nightgryphon/LInTech-network/Server-IBM-PC/Reference_Photo/MCU_Night_Gryphon.jpeg

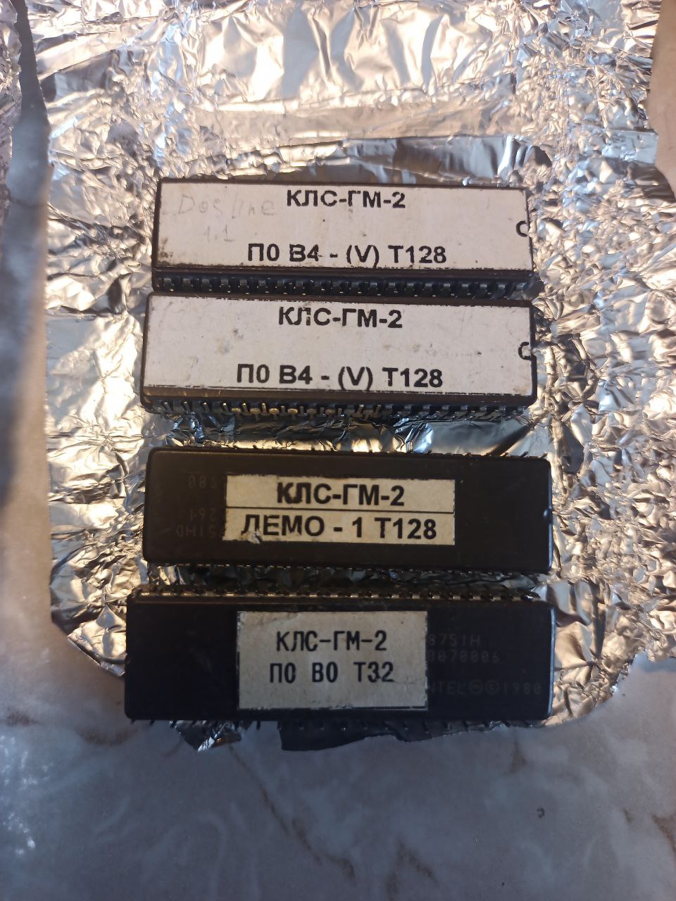
Server-IBM-PC/Reference_Photo/MCU_Night_Gryphon.jpeg
