nightgryphon/LInTech-network/Server-IBM-PC/Reference_Photo/NC-ACM-2.2-1994_Arseny-UKNC.narod.ru/01_NC-ACM-2.2-1994_Front_Photo.jpg

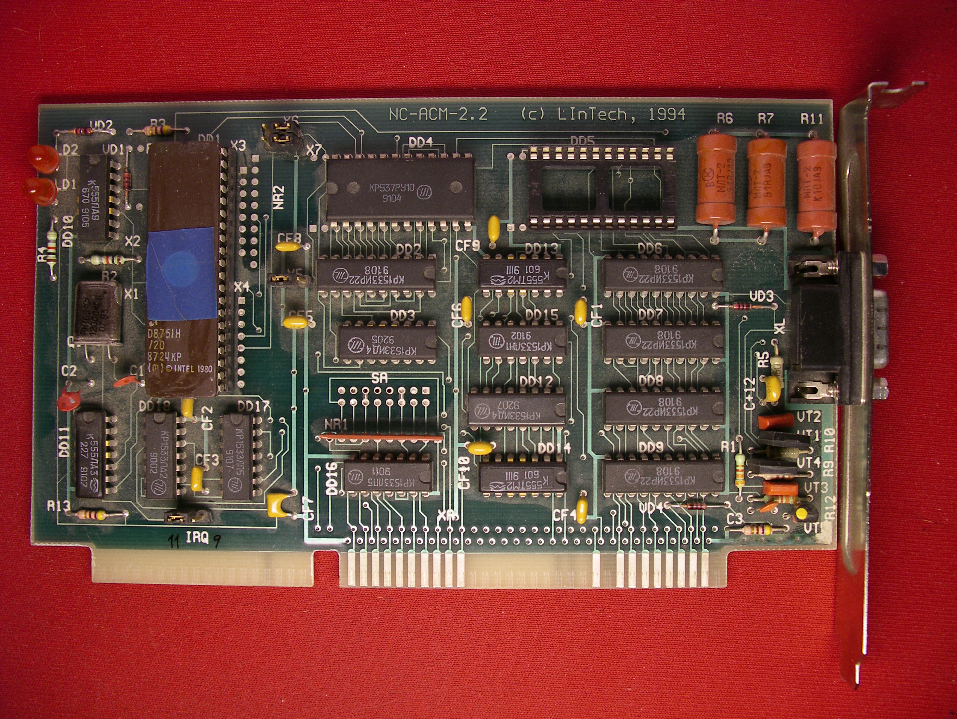
Server-IBM-PC/Reference_Photo/NC-ACM-2.2-1994_Arseny-UKNC.narod.ru/01_NC-ACM-2.2-1994_Front_Photo.jpg
