nightgryphon/LInTech-network/Server-IBM-PC/Reference_Photo/NC-ACM-2.2-1994_Arseny-UKNC.narod.ru/02_NC-ACM-2.2-1994_Back_Photo.jpg

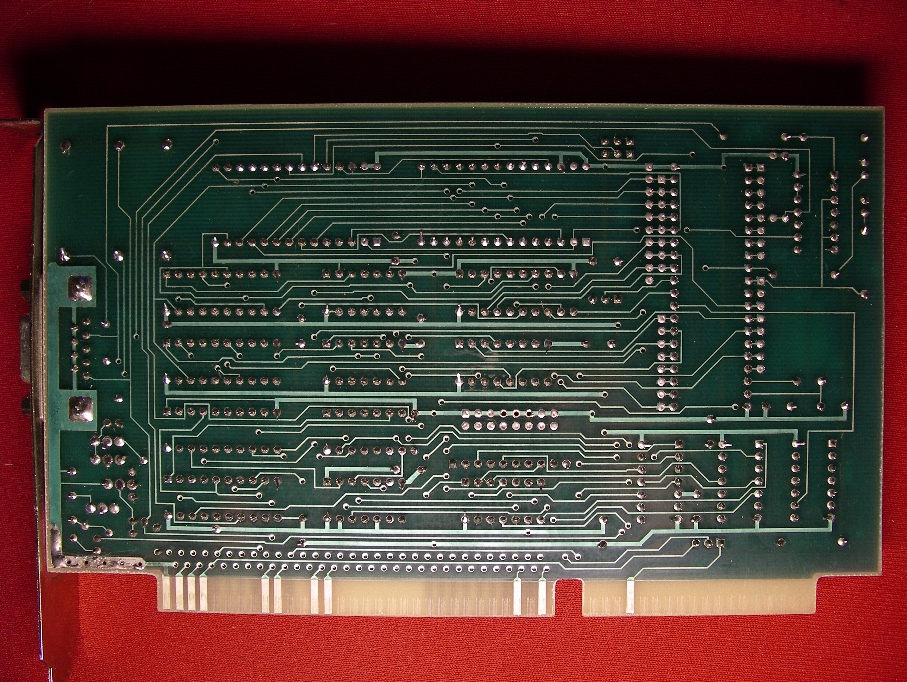
Server-IBM-PC/Reference_Photo/NC-ACM-2.2-1994_Arseny-UKNC.narod.ru/02_NC-ACM-2.2-1994_Back_Photo.jpg
