nightgryphon/LInTech-network/Server-IBM-PC/Reference_Photo/NC-ACM-2.2-1994_Arseny-UKNC.narod.ru/03_NC-ACM-2.2-1994_Front_Photo_Tracks.jpg

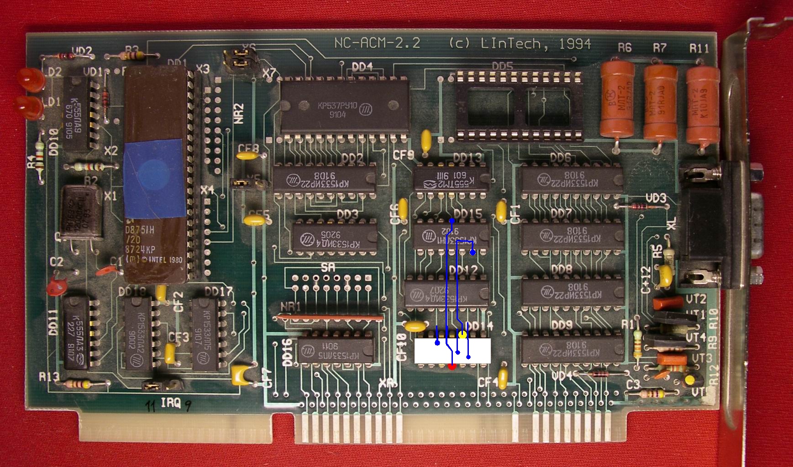
Server-IBM-PC/Reference_Photo/NC-ACM-2.2-1994_Arseny-UKNC.narod.ru/03_NC-ACM-2.2-1994_Front_Photo_Tracks.jpg
