nightgryphon/LInTech-network/Server-IBM-PC/Reference_Photo/NC-ACM-2.3E-1996_Serebriakov_aka_PaulArgent/05_NC-ACM-2.3E-1996_Front_Photo_MCU.jpg

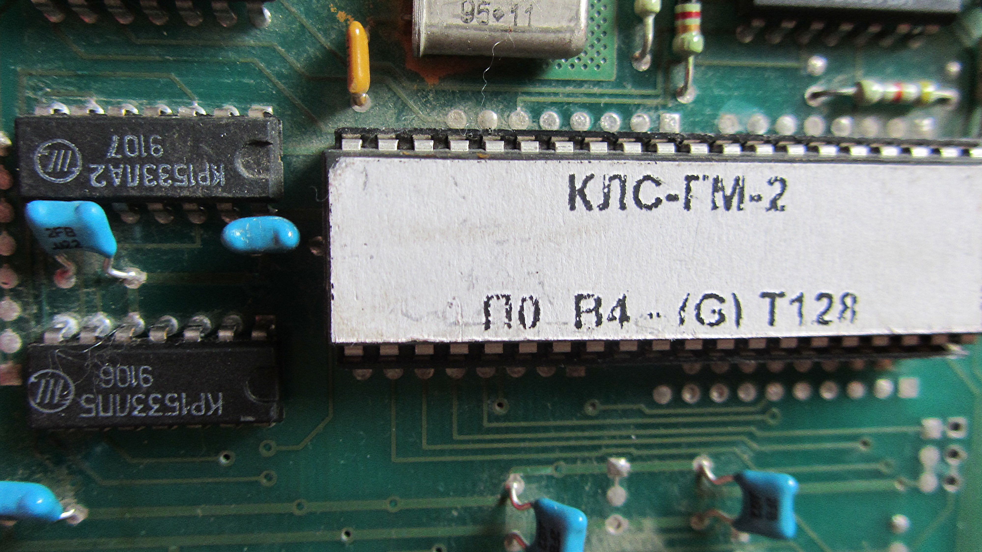
Server-IBM-PC/Reference_Photo/NC-ACM-2.3E-1996_Serebriakov_aka_PaulArgent/05_NC-ACM-2.3E-1996_Front_Photo_MCU.jpg
