nightgryphon/LInTech-network/Server-IBM-PC/Reference_Photo/NC-ACM-2.3E-1996_Serebriakov_aka_PaulArgent/07_NC-ACM-2.3E-1996_Back_Photo.jpg

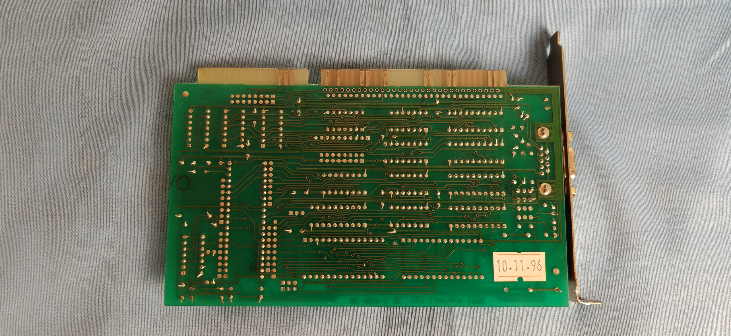
Server-IBM-PC/Reference_Photo/NC-ACM-2.3E-1996_Serebriakov_aka_PaulArgent/07_NC-ACM-2.3E-1996_Back_Photo.jpg
