nightgryphon/LInTech-network/Terminal-BK0010/Reference_Photo/NC-IFM-H1.0-1995_Night_Gryphon/02_NC-IFM-H1.0-1995-Back-Scan.jpg

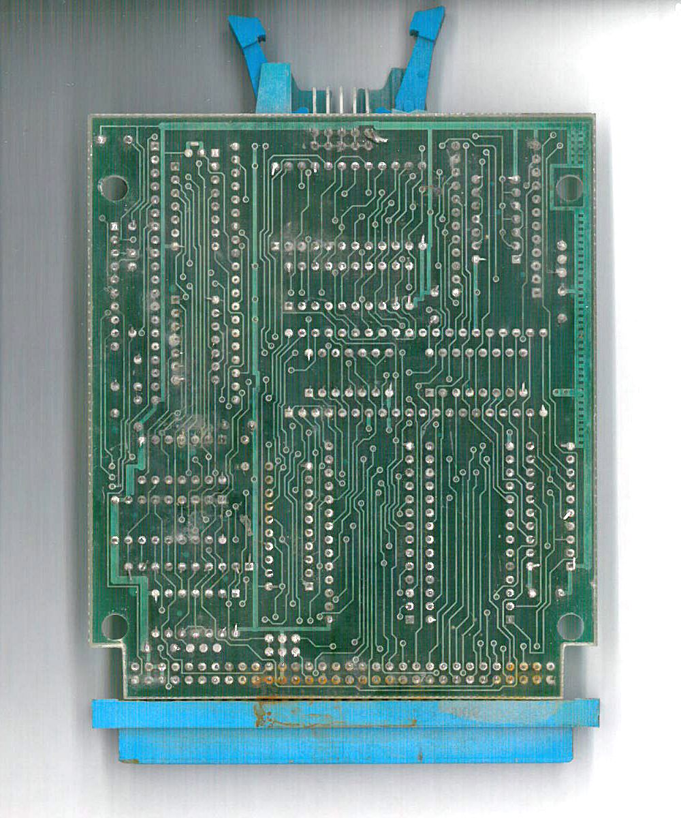
Terminal-BK0010/Reference_Photo/NC-IFM-H1.0-1995_Night_Gryphon/02_NC-IFM-H1.0-1995-Back-Scan.jpg
