nightgryphon/LInTech-network/Terminal-Corvette/Reference_Photo/NC-IFM-2.1-1993_Anton_Mironov_Front_MCU.jpg

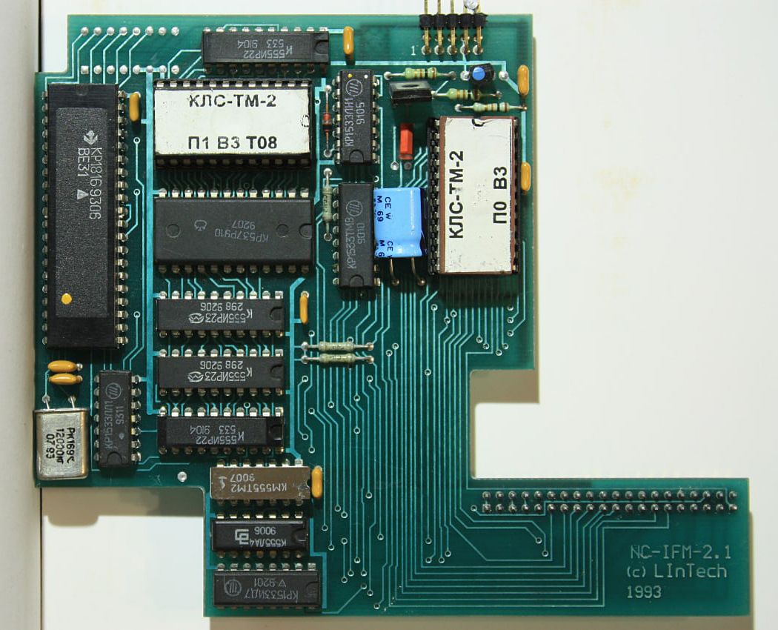
Terminal-Corvette/Reference_Photo/NC-IFM-2.1-1993_Anton_Mironov_Front_MCU.jpg
