nightgryphon/LInTech-network/Terminal-Corvette/Reference_Photo/NC-IFM-2.1-1993_lordamot_aka_Sergey_Lemeshev/01_NC-IFM-2.1-1993_Front_Scan.png

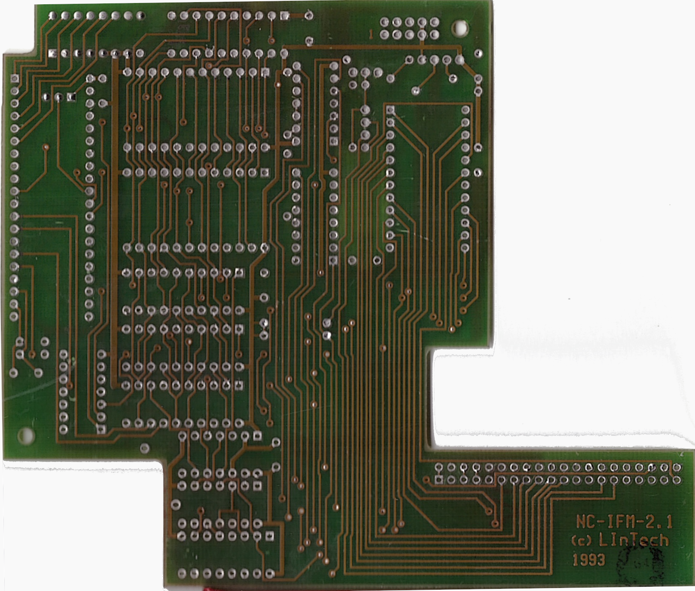
Terminal-Corvette/Reference_Photo/NC-IFM-2.1-1993_lordamot_aka_Sergey_Lemeshev/01_NC-IFM-2.1-1993_Front_Scan.png
