nightgryphon/LInTech-network/Terminal-Corvette/Reference_Photo/NC-IFM-2.1-1993_lordamot_aka_Sergey_Lemeshev/05_NC-IFM-2.1-1993_Photo_Connection.jpg

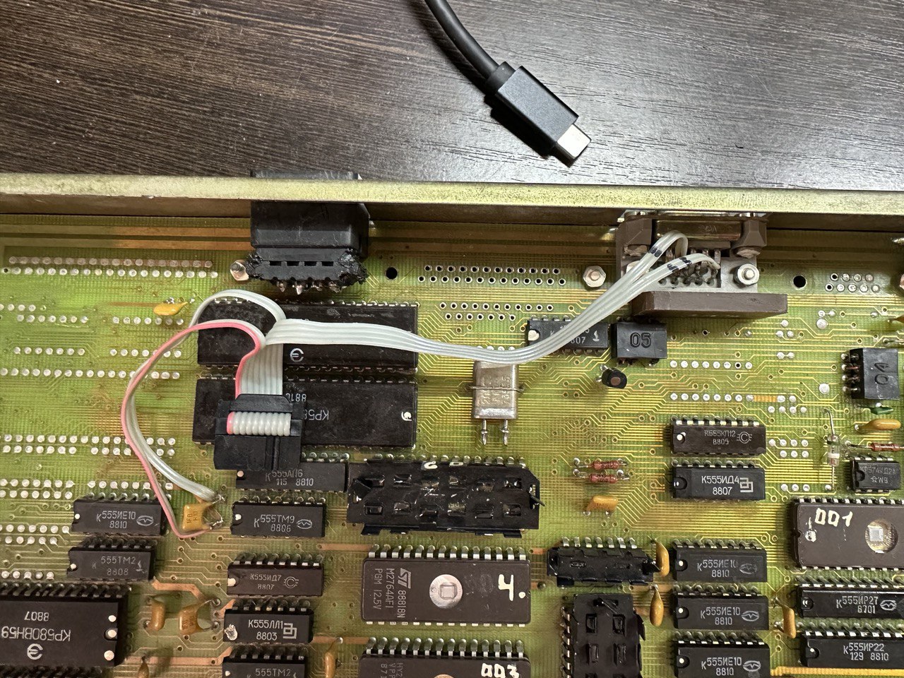
Terminal-Corvette/Reference_Photo/NC-IFM-2.1-1993_lordamot_aka_Sergey_Lemeshev/05_NC-IFM-2.1-1993_Photo_Connection.jpg
