nightgryphon/LInTech-network/Terminal-Corvette/Reference_Photo/NC-IFM-2.1-1993_lordamot_aka_Sergey_Lemeshev/07_NC-IFM-2.1-1993_Photo_EPROM-P1-Left.jpg

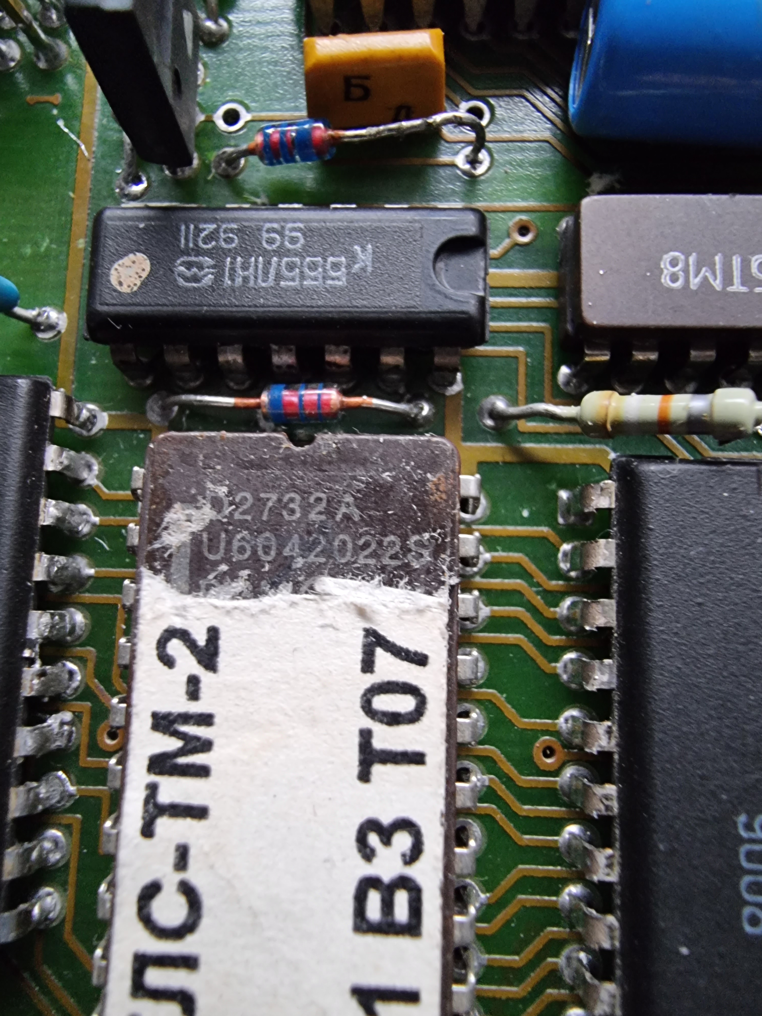
Terminal-Corvette/Reference_Photo/NC-IFM-2.1-1993_lordamot_aka_Sergey_Lemeshev/07_NC-IFM-2.1-1993_Photo_EPROM-P1-Left.jpg
