nightgryphon/LInTech-network/Terminal-UKNC/Reference_Photo/NC-IFM-B1.0-1994_Arseny-UKNC.narod.ru/NC-IFM-B1.0-1994_Front_Photo.jpg

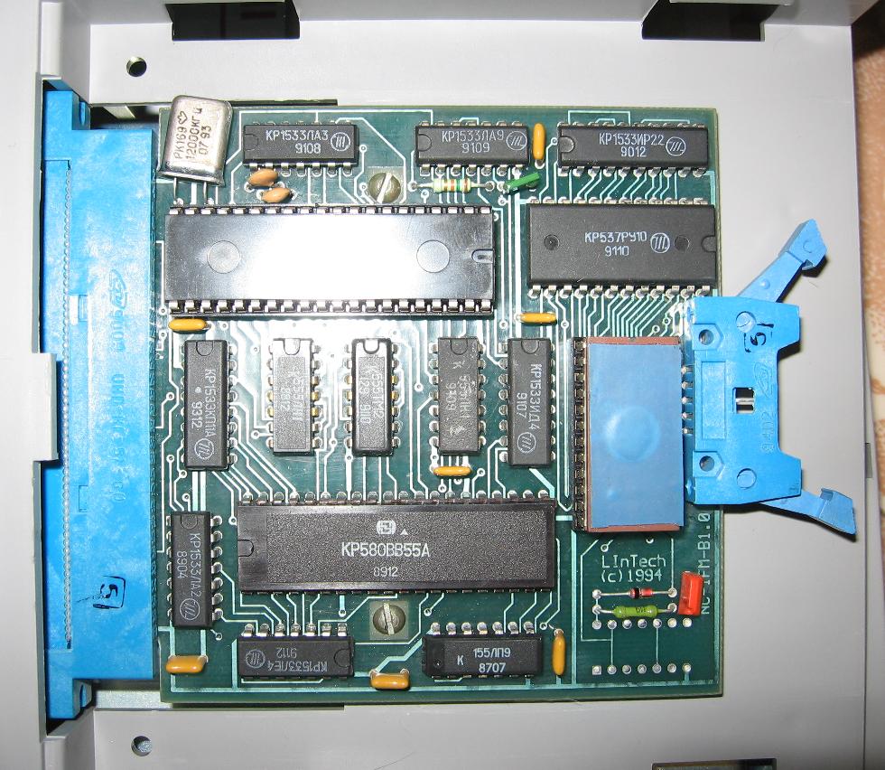
Terminal-UKNC/Reference_Photo/NC-IFM-B1.0-1994_Arseny-UKNC.narod.ru/NC-IFM-B1.0-1994_Front_Photo.jpg
