nightgryphon/LInTech-network/Terminal-UKNC/Reference_Photo/NC-IFM-B1.0-1994_Night_Gryphon/02_NC-IFM-B1.0-1994_Back_Scan.jpg

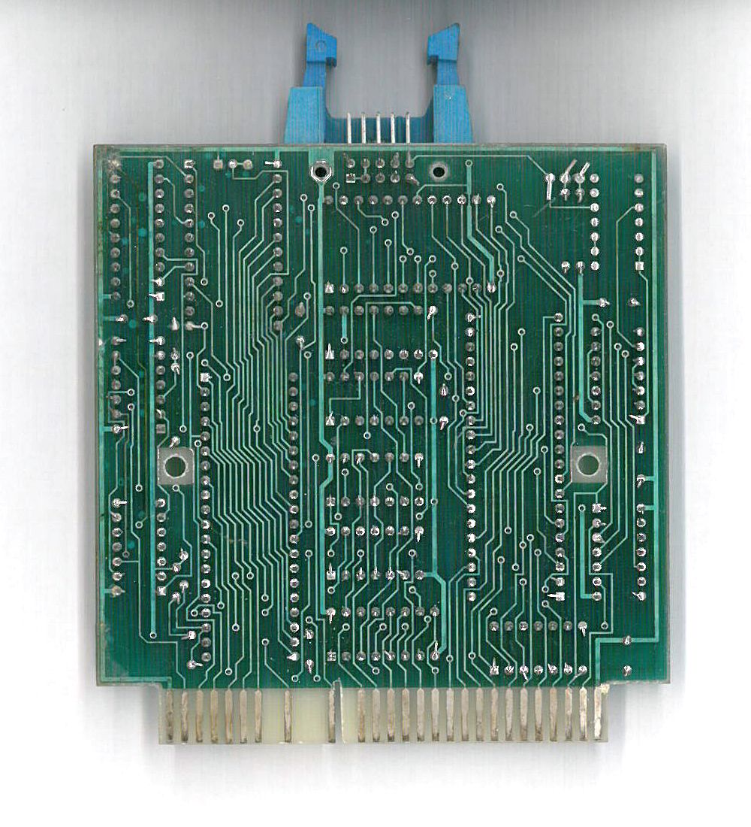
Terminal-UKNC/Reference_Photo/NC-IFM-B1.0-1994_Night_Gryphon/02_NC-IFM-B1.0-1994_Back_Scan.jpg
