nightgryphon/LInTech-network/Terminal-Corvette/Reference_Photo/NC-IFM-2.1-1993_Serebriakov_aka_PaulArgent/01_PCB_07.12.97-ONE_EPROM/07_NC-IFM-2.1-1993_Photo_Installed_new_label.jpg

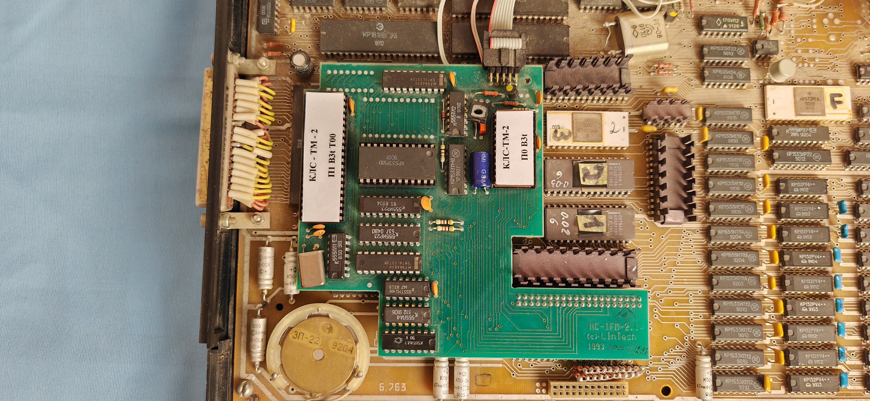
Terminal-Corvette/Reference_Photo/NC-IFM-2.1-1993_Serebriakov_aka_PaulArgent/01_PCB_07.12.97-ONE_EPROM/07_NC-IFM-2.1-1993_Photo_Installed_new_label.jpg
