nightgryphon/LInTech-network/Terminal-Corvette/Reference_Photo/NC-IFM-2.1-1993_Serebriakov_aka_PaulArgent/02_PCB_18.11.97/04_NC-IFM-2.1-1993_Photo_Installed.jpg

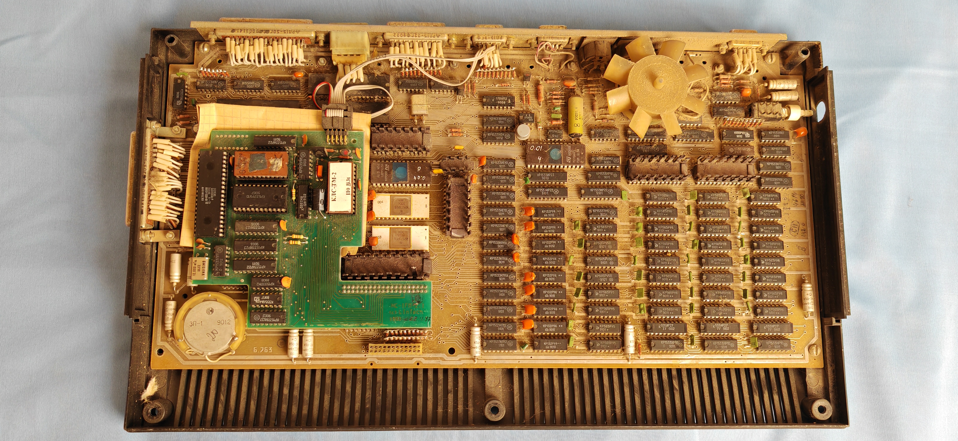
Terminal-Corvette/Reference_Photo/NC-IFM-2.1-1993_Serebriakov_aka_PaulArgent/02_PCB_18.11.97/04_NC-IFM-2.1-1993_Photo_Installed.jpg
