nightgryphon/LInTech-network/Terminal-Corvette/Reference_Photo/NC-IFM-2.1-1993_Serebriakov_aka_PaulArgent/03_PCB_13.11.97/03_NC-IFM-2.1-1993_Back_Scan.jpg

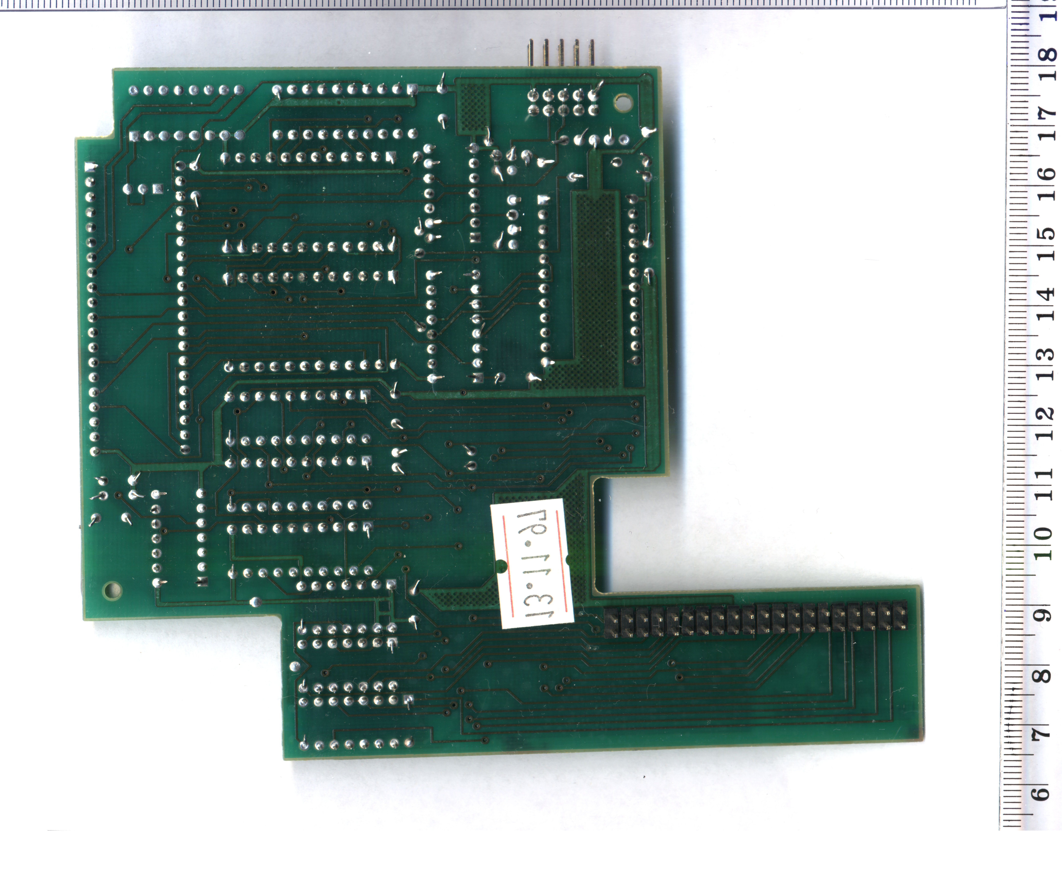
Terminal-Corvette/Reference_Photo/NC-IFM-2.1-1993_Serebriakov_aka_PaulArgent/03_PCB_13.11.97/03_NC-IFM-2.1-1993_Back_Scan.jpg
