nightgryphon/LInTech-network/Terminal-Corvette/Reference_Photo/NC-IFM-2.1-1993_Serebriakov_aka_PaulArgent/04_PCB_01.05.97/02_NC-IFM-2.1-1993_Front_Scan.jpg

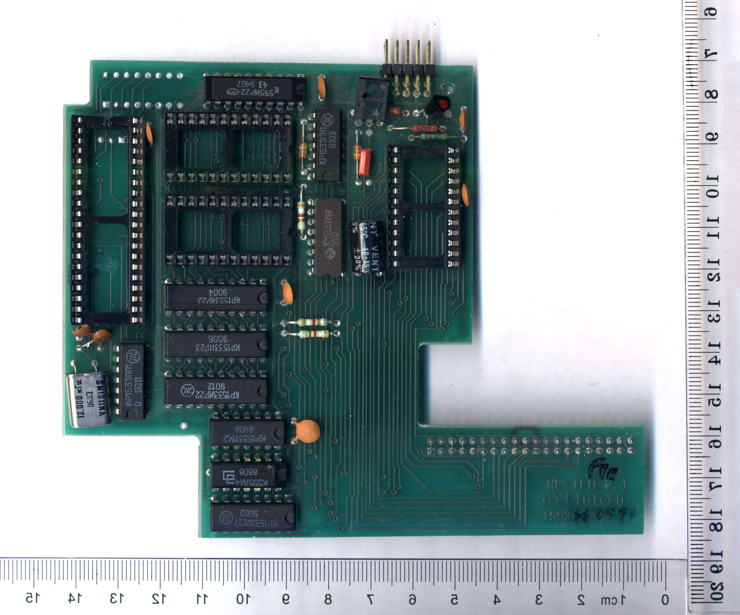
Terminal-Corvette/Reference_Photo/NC-IFM-2.1-1993_Serebriakov_aka_PaulArgent/04_PCB_01.05.97/02_NC-IFM-2.1-1993_Front_Scan.jpg
