nightgryphon/LInTech-network/Terminal-Corvette/Reference_Photo/NC-IFM-2.1-1993_Serebriakov_aka_PaulArgent/04_PCB_01.05.97/03_NC-IFM-2.1-1993_Back_Scan.jpg

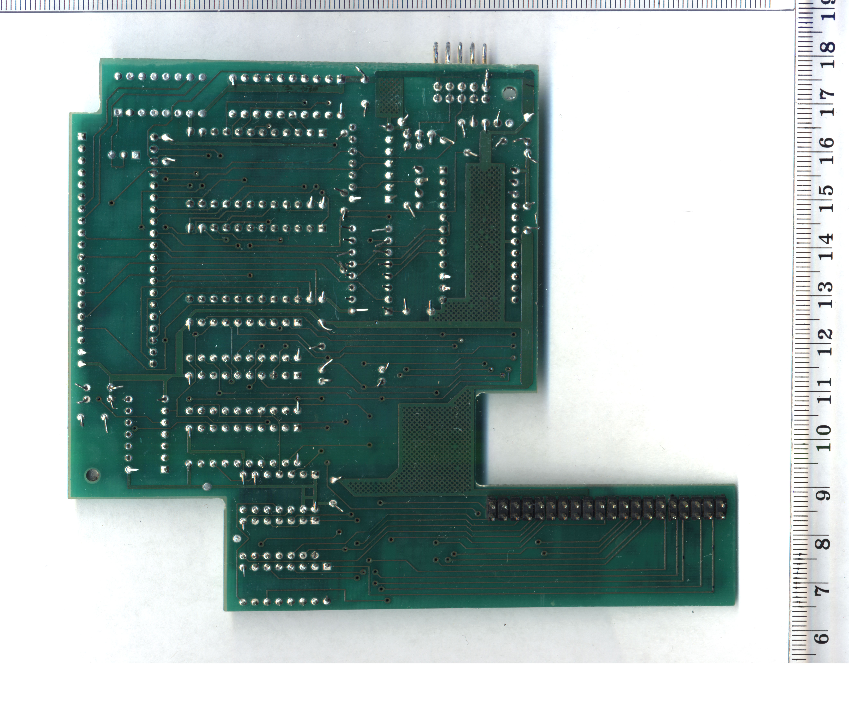
Terminal-Corvette/Reference_Photo/NC-IFM-2.1-1993_Serebriakov_aka_PaulArgent/04_PCB_01.05.97/03_NC-IFM-2.1-1993_Back_Scan.jpg
